steferic/world-radio/hardware/prototype/schematics/world_radio.kicad_sch

## KiCad design hardware/prototype/schematics/world_radio.kicad_sch (2026-06-25)

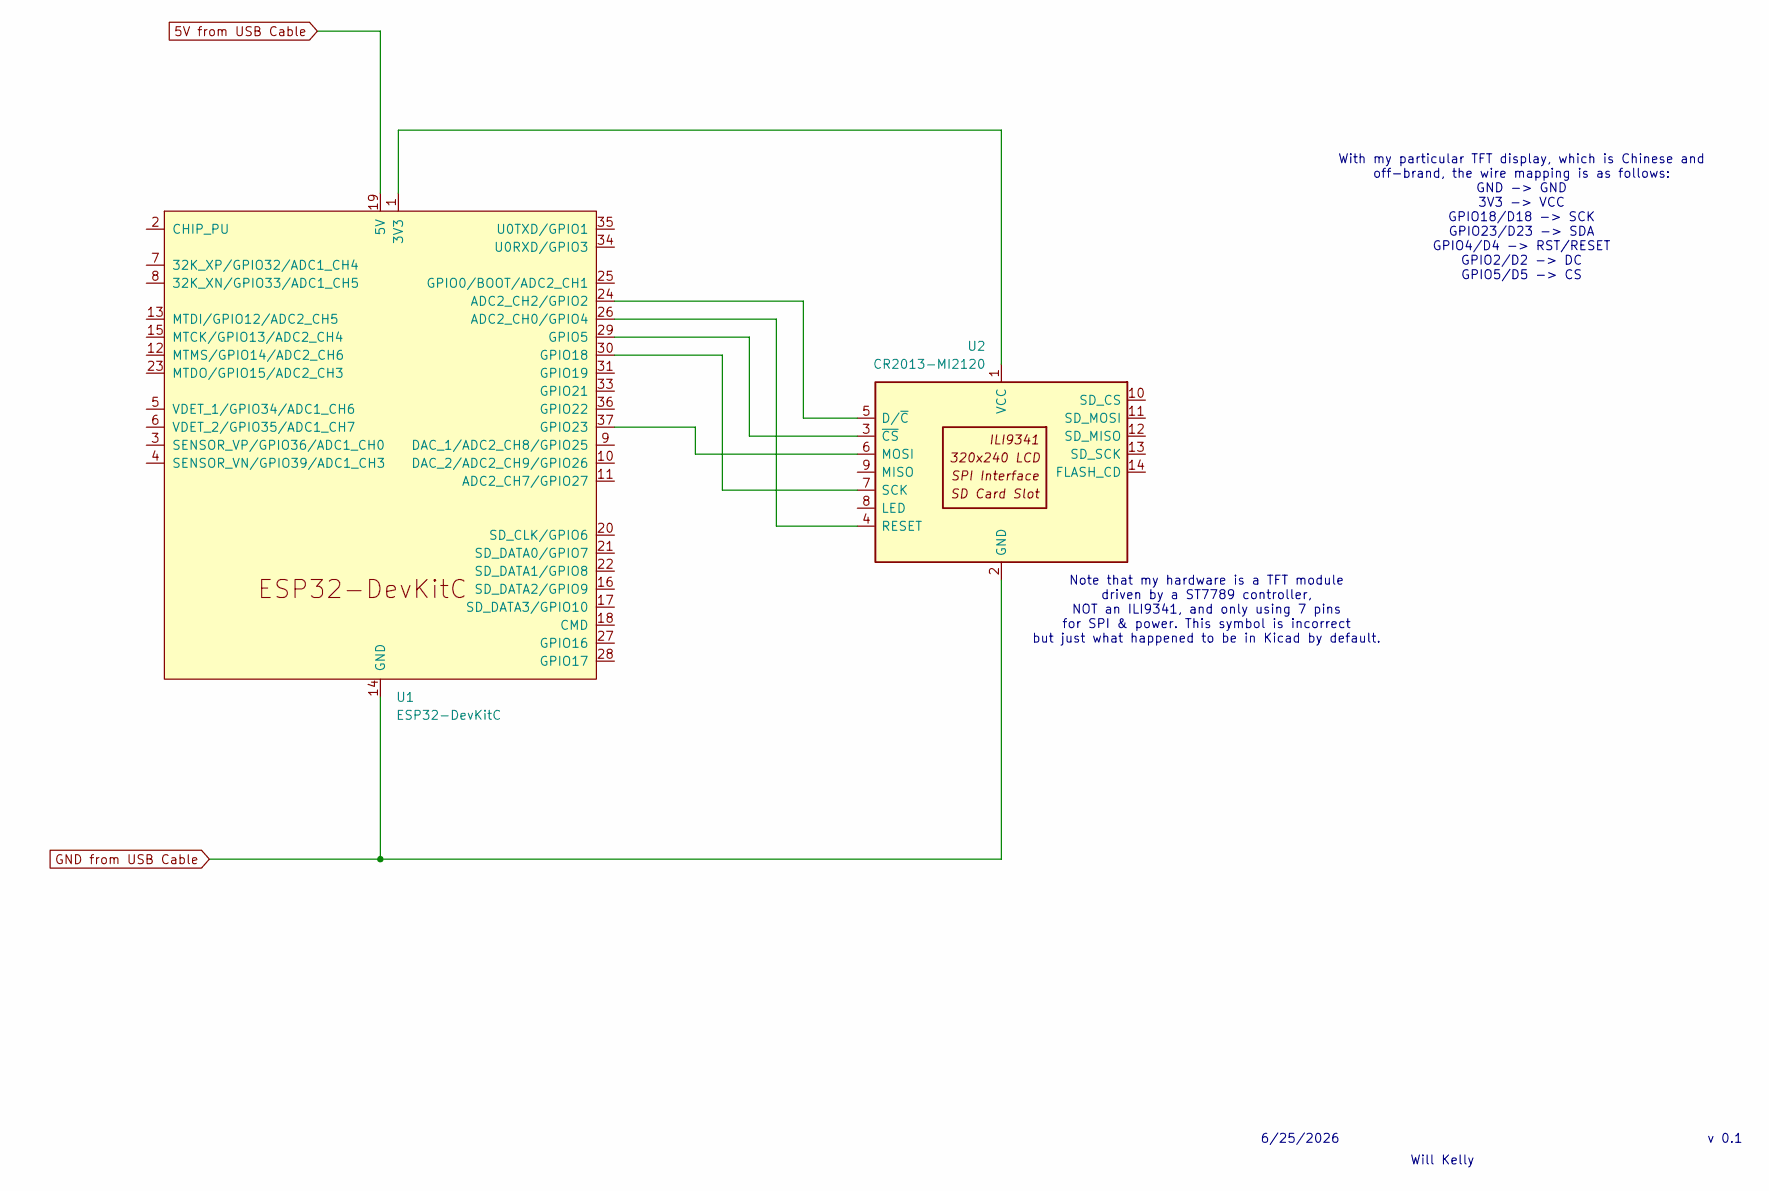
[picture p2: schematic world_radio.kicad_sch]

Parts:
U1: ESP32-DevKitC
U2: CR2013-MI2120

Connections:
5V from USB Cable: U1.19 (5V)
GND from USB Cable: U1.14 (GND), U1.32 (GND), U1.38 (GND), U2.2 (GND)
unnamed: U1.1 (3V3), U2.1 (VCC)
unnamed: U1.24 (ADC2_CH2/GPIO2), U2.5 (D/~C)
unnamed: U1.26 (ADC2_CH0/GPIO4), U2.4 (RESET)
unnamed: U1.29 (GPIO5), U2.3 (~CS)
unnamed: U1.30 (GPIO18), U2.7 (SCK)
unnamed: U1.37 (GPIO23), U2.6 (MOSI)

Notes on the sheet:
Will Kelly
6/25/2026
v 0.1
With my particular TFT display, which is Chinese and off-brand, the wire mapping is as follows: GND -> GND 3V3 -> VCC GPIO18/D18 -> SCK GPIO23/D23 -> SDA GPIO4/D4 -> RST/RESET GPIO2/D2 -> DC GPIO5/D5 -> CS
Note that my hardware is a TFT module driven by a ST7789 controller, NOT an ILI9341, and only using 7 pins for SPI & power. This symbol is incorrect but just what happened to be in Kicad by default.
